trcclub/HardSense/Hardware/Kicad/PCB for ESP32 w 38 Pins/HardSense_PCB_001.jpg

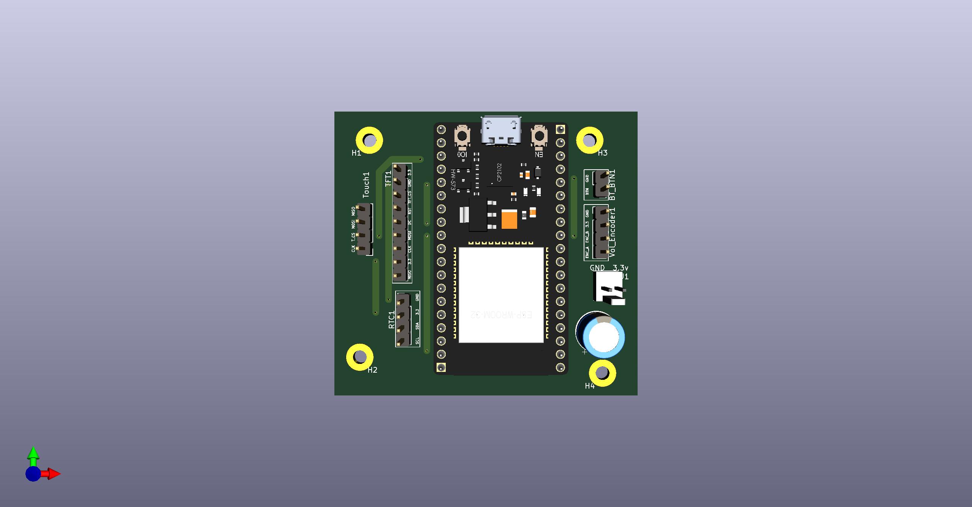
Hardware/Kicad/PCB for ESP32 w 38 Pins/HardSense_PCB_001.jpg
