trcclub/HardSense/HardSenseESP - 001.jpg

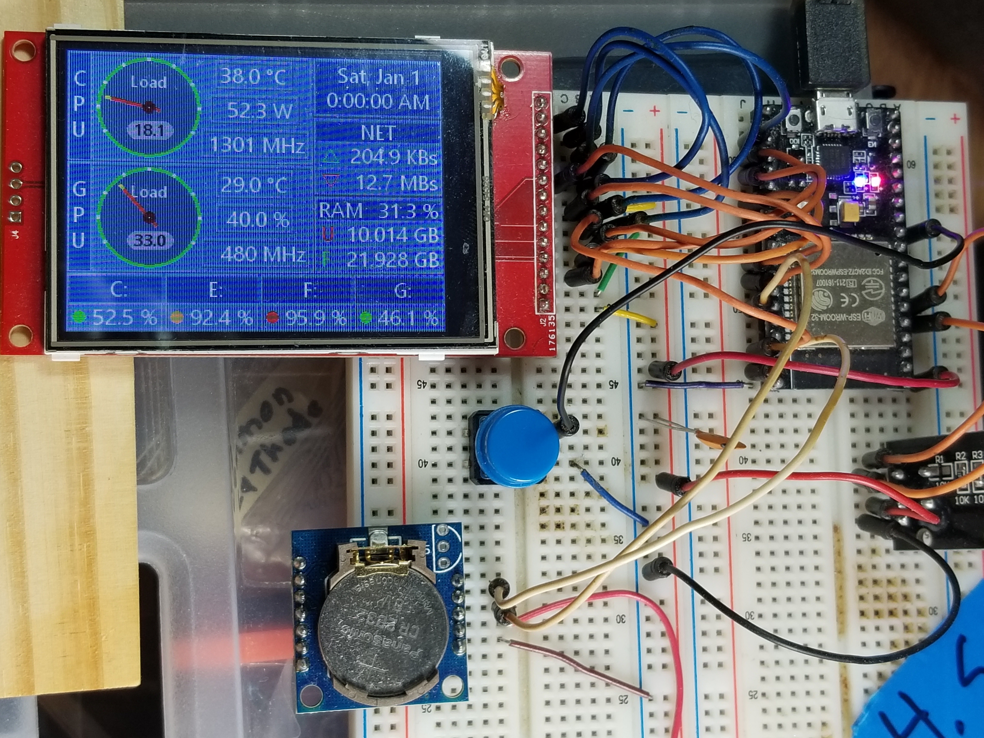
HardSenseESP - 001.jpg
