trcclub/HardSense/HardSenseESP_Prototype_001.jpg

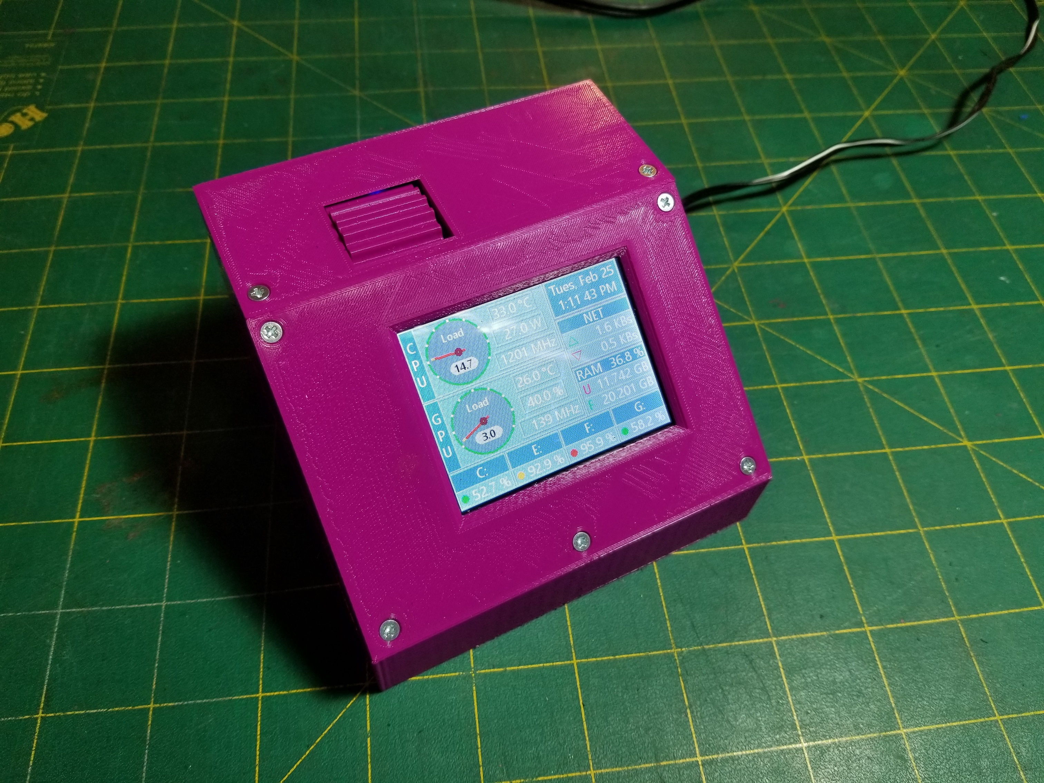
HardSenseESP_Prototype_001.jpg
