trcclub/HardSense/HardSenseESP_Prototype_002.jpg

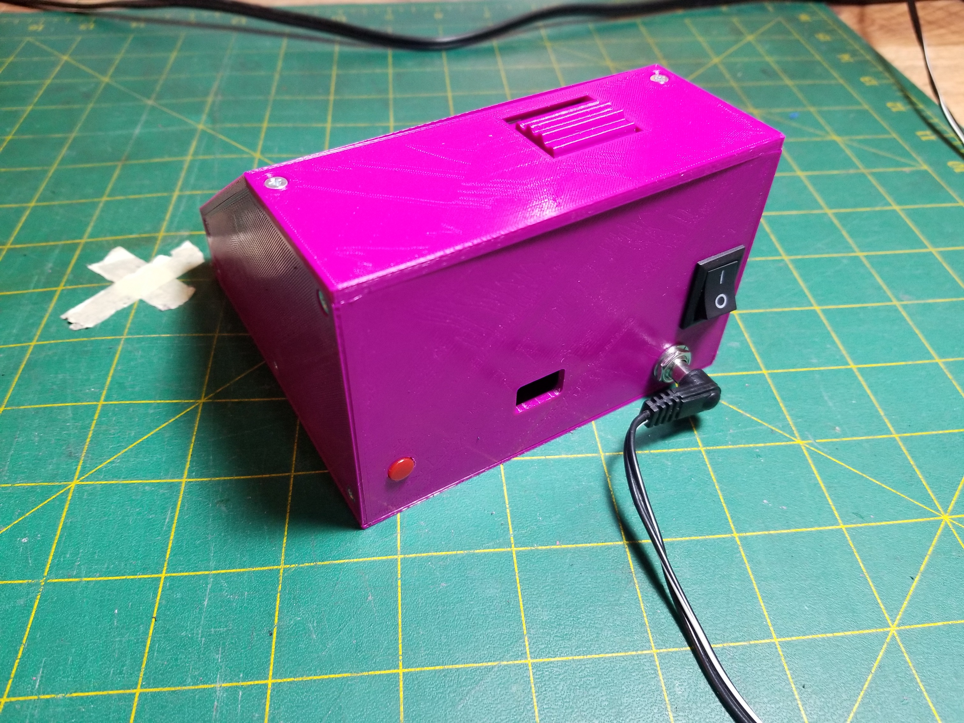
HardSenseESP_Prototype_002.jpg
