trcclub/HardSense/HardSenseESP_Prototype_003.jpg

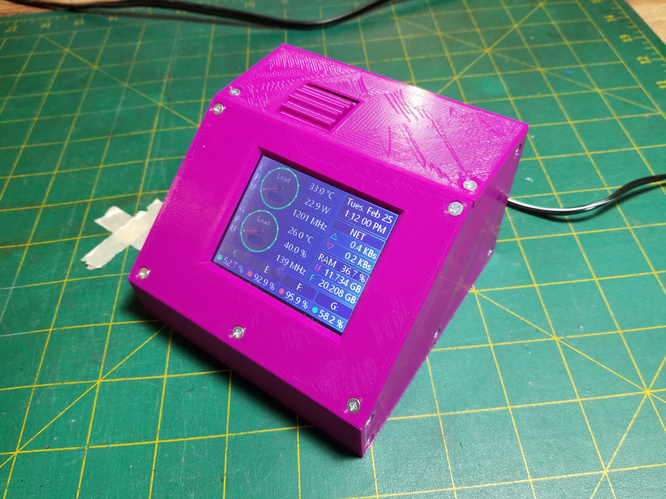
HardSenseESP_Prototype_003.jpg
