trcclub/HardSense/HardSenseESP_Prototype_004.jpg

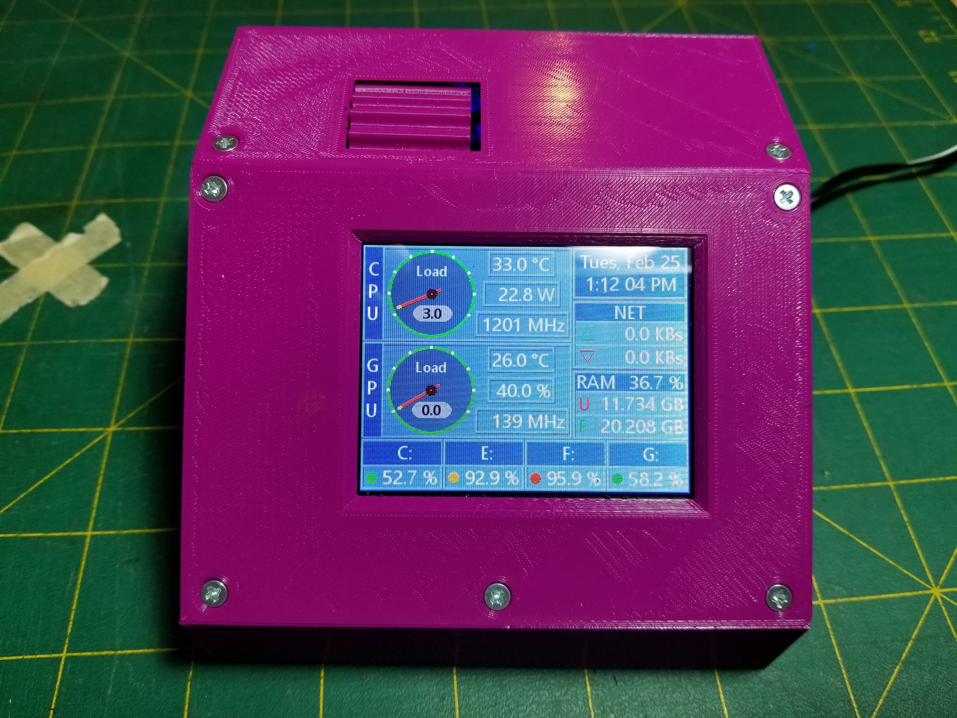
HardSenseESP_Prototype_004.jpg
