trcclub/HardSense/Hardware/Kicad/ESP32S - 30 Pin - Pin Out Mapping.jpg

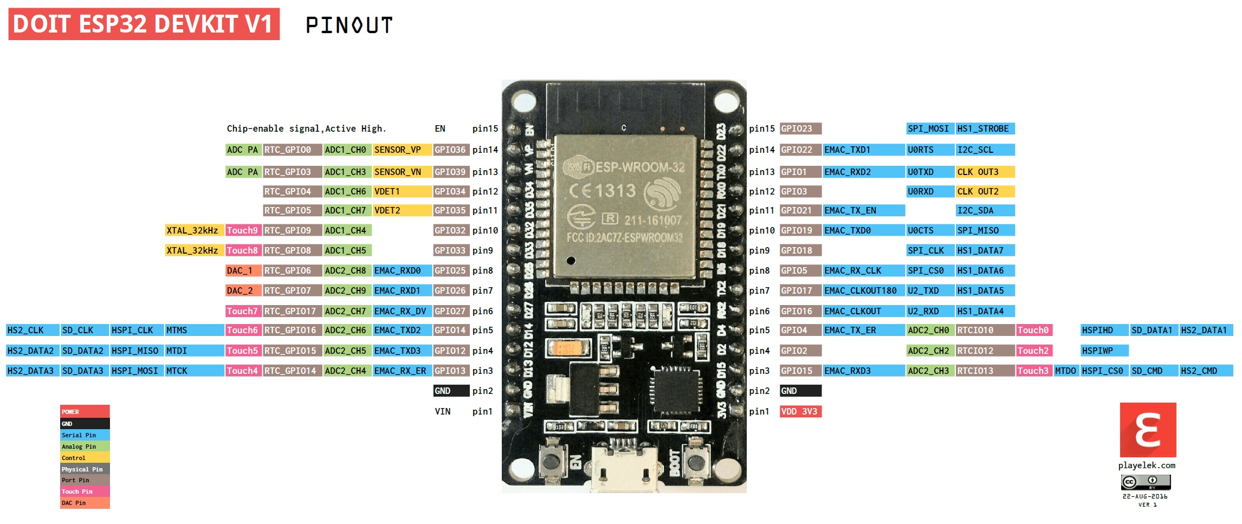
Hardware/Kicad/ESP32S - 30 Pin - Pin Out Mapping.jpg
