trcclub/HardSense/Hardware/Kicad/HardSense_PCB_ESP32S_001.jpg

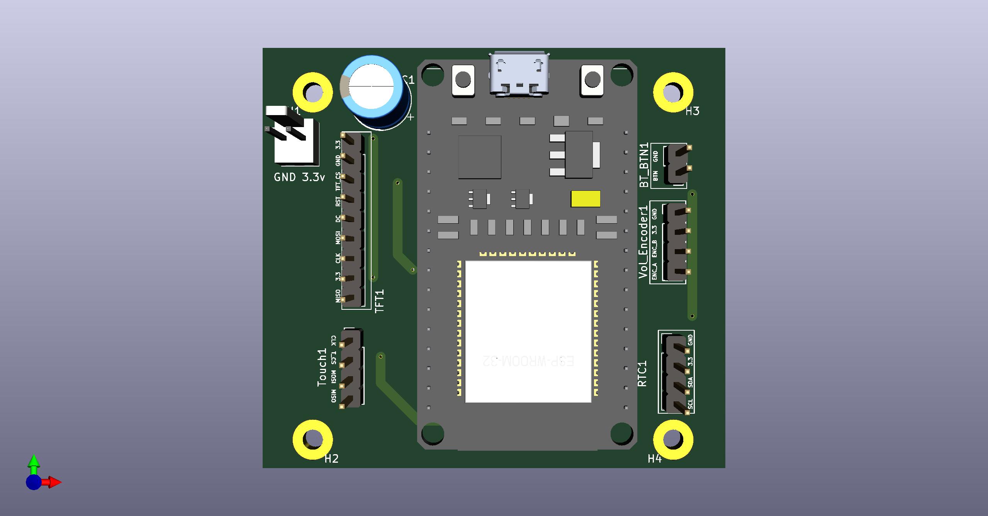
Hardware/Kicad/HardSense_PCB_ESP32S_001.jpg
