trcclub/HardSense/Hardware/Kicad/HardSense_PCB_ESP32S_002.jpg

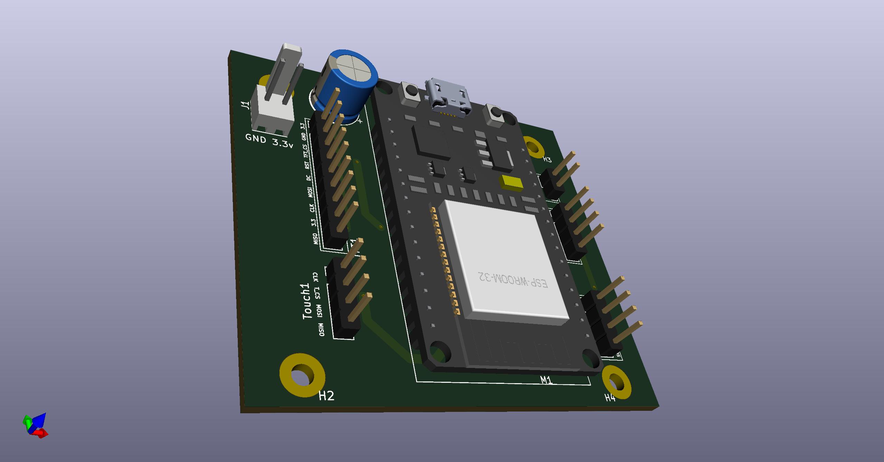
Hardware/Kicad/HardSense_PCB_ESP32S_002.jpg
