trcclub/HardSense/OTA Updates on HardSense.jpg

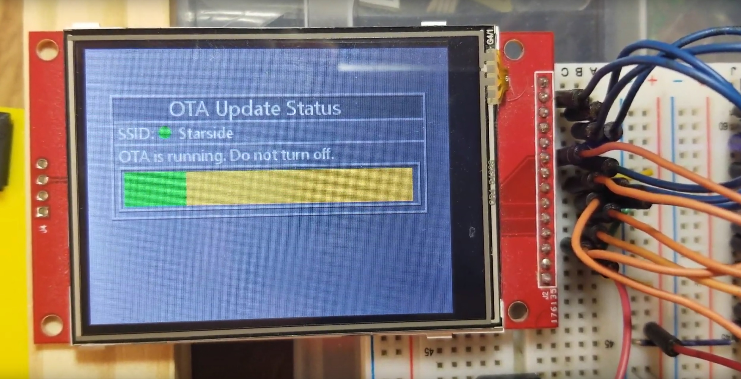
OTA Updates on HardSense.jpg
