trcclub/HardSense/Software/ESP32/Processing_Font_Settings.jpg

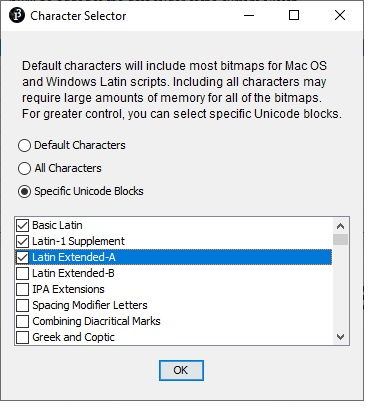
Software/ESP32/Processing_Font_Settings.jpg
