trcclub/HardSense/Software/Windows/Pics/HardSenseESP_HomeScreen.jpg

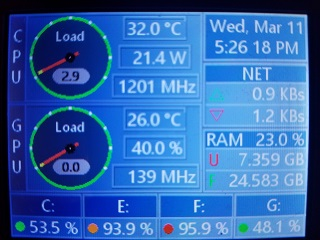
Software/Windows/Pics/HardSenseESP_HomeScreen.jpg
