trcclub/HardSense/Software/Windows/Pics/HardSenseESP_HomeScreen_-_CPU_Panel.jpg

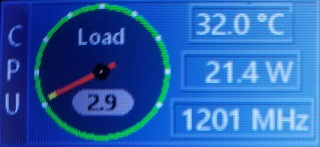
Software/Windows/Pics/HardSenseESP_HomeScreen_-_CPU_Panel.jpg
