trcclub/HardSense/Software/ESP32/HardSenseESP/src/DisplayHandler/GUI/HS_SplashScreen.h

#pragma once
#include "HS_ScreenBase.h"

#define TEXT_COLOR 0xCE59
#define PANEL_HCOLOR 0x5AEB
#define PANEL_BGCOLOR 0x738E
#define BOX_BORDER_COLOR 0x9CD3
#define BOX_DROP_SHADOW 0x4208

#define NET_PANEL_X 0
#define NET_PANEL_Y 40

#define SERVER_PANEL_X 0
#define SERVER_PANEL_Y 85

class HS_SplashScreen :
	public HS_ScreenBase
{
private:
	HS_Theme splashScreenTheme;

	unsigned long lastUpdate = 0;
	int updateScreenInterval = 15;

	void UpdateCircle();
	int circleLoopCounter;	
	int secondaryLoopCounter;
	uint32_t col[8];

	void Draw_NetworkConnectionPanel();
	void Update_ConnectingToNetwork(String netID);
	void Update_ConnectedToNetwork(String netID);
	void Update_NetworkConnectionInfo(String netID, uint16_t circleColor);
	
	void Draw_ServerConnectionPanel();
	void Update_ConnectingToServer(String serverID);

public:
	HS_SplashScreen(Queues *newQueues, TFT_eSPI* newTFT);
	~HS_SplashScreen();
	void UpdateScreen(String value);
	void UpdateScreenOnInterval();
};
