trcclub/HardSense/Software/ESP32/HardSenseESP/src/DisplayHandler/GUI/HomeScreen_Functions.h

#pragma once
#include "HS_HomeScreen.h"
#include "../../QueueItem.h"

HS_HomeScreen* HS_Current_HomeScreen = NULL;

void Create_HomeScreen(Queues *newQueues, TFT_eSPI *TFT) {
	HS_Current_HomeScreen = new HS_HomeScreen(newQueues, TFT);
}

void Destroy_HomeScreen()
{
	if (HS_Current_HomeScreen != NULL)
	{
		delete(HS_Current_HomeScreen);
		HS_Current_HomeScreen = NULL;
	}
}

void Update_HomeScreen(String value)
{
	HS_Current_HomeScreen->UpdateScreen(value);
}

void Update_HomeScreen_OnInterval()
{
	HS_Current_HomeScreen->UpdateScreenOnInterval();
}

bool Handle_HomeScreen_Touch(int x, int y)
{
	HS_Current_HomeScreen->HandleTouch(x, y);
}
