trcclub/HardSense/Software/ESP32/HardSenseESP/DisplayHandler/GUI/HS_HomeScreen_B.h

#pragma once
#include "HS_ScreenBase.h"
#include "Widgets/HS_Dial_Widget.h"

#define SCREEN_HOME_LOAD_DIAL_MIN -120
#define SCREEN_HOME_LOAD_DIAL_MAX 120

#define SCREEN_HOME_CPU_LOAD_DIAL_X 22
#define SCREEN_HOME_CPU_LOAD_DIAL_Y 2

#define PANEL_HCOLOR 0x3BB6
#define PANEL_BGCOLOR 0x7D19
#define BOX_BORDER_COLOR 0x9DDB
#define BOX_DROP_SHADOW 0x63F2

#define CPU_PANEL_LOW_X 0
#define CPU_PANEL_HIGH_X 208
#define CPU_PANEL_LOW_Y 0
#define CPU_PANEL_HIGH_Y 94


class HS_HomeScreen_B :
	public HS_ScreenBase
{
private:
	HS_Dial_Widget* cpuLoadWidget;
	uint16_t Home_Screen_cpuLoadDial_CurrentRingColor;

	//HS_Dial_Widget* gpuLoadWidget;
	//uint16_t Home_Screen_gpuLoadDial_CurrentRingColor;

	void Draw_CPU_Panel();
	void Update_CPU_Panel_Load(double percentage);
	bool CPU_Panel_Touched(int x, int y);


	TFT_eSprite* textPrinter_Sprite;

	void Draw_Net_Panel();
	void Update_Net_DownloadSpeed(double dSpeed);
	void Update_Net_UpLoadSpeed(double uSpeed);
	String GetSpeedString(double speed);

public:
	HS_HomeScreen_B(TFT_eSPI* newTFT);
	~HS_HomeScreen_B();
	void UpdateScreen(String value);
	void SetSensorList(void(*AddItemToOutputQueue_func)(char key, String value));
	void HandleTouch(int x, int y);

};
